dilyar-arkin/Spaceys/software_development_files/test_cases/BMP280_pressure_sensor_test.py

from machine import I2C, Pin
import time
from time import sleep
import utime
from pico_i2c_lcd import I2cLcd
from machine import ADC
from bmp280 import BMP280
from bmp280_configuration import BMP280Configuration
from bmp280_i2c import BMP280I2C
#from bmp280_init_class import *

try:
    i2c0_sda = Pin(2)
    i2c0_scl = Pin(3)
    i2c0 = I2C(1, sda=i2c0_sda, scl=i2c0_scl, freq=400000)
        
except Exception as e:
    print("Error found initializing I2C bus:", e)
    raise SystemExit
    
try:
    devices = i2c0.scan()
    print("Detected devices:")
    for device in devices:
        print(hex(device))
        bmp280_i2c = BMP280I2C(0x77, i2c0) #address may be different
except Exception as e:
    print("Error initializing BMP280 sensor:", e)
    raise SystemExit

while True:
    try:
        temperature = read_temperature(bmp280_i2c)
        print(f"T: {round(temperature,2)} °C")       
    except Exception as e:
        print("Error found:", e)
        raise SystemExit
    finally:
        sleep(1)
